siliconchris1973/fairytale/3rd Party Schematics/LED5RG2PIN_Dimension.jpg

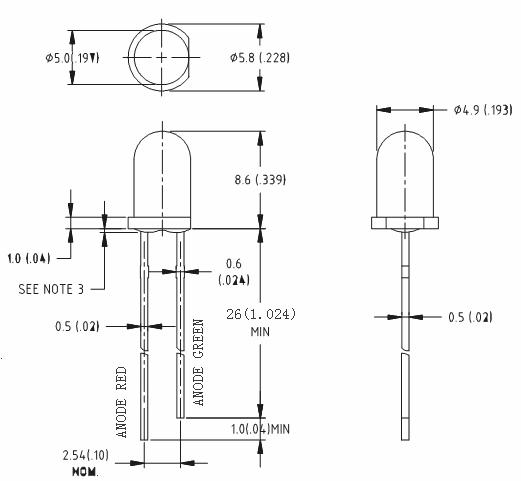
3rd Party Schematics/LED5RG2PIN_Dimension.jpg
