siliconchris1973/fairytale/Pics for V2/NFC-Backside.jpg

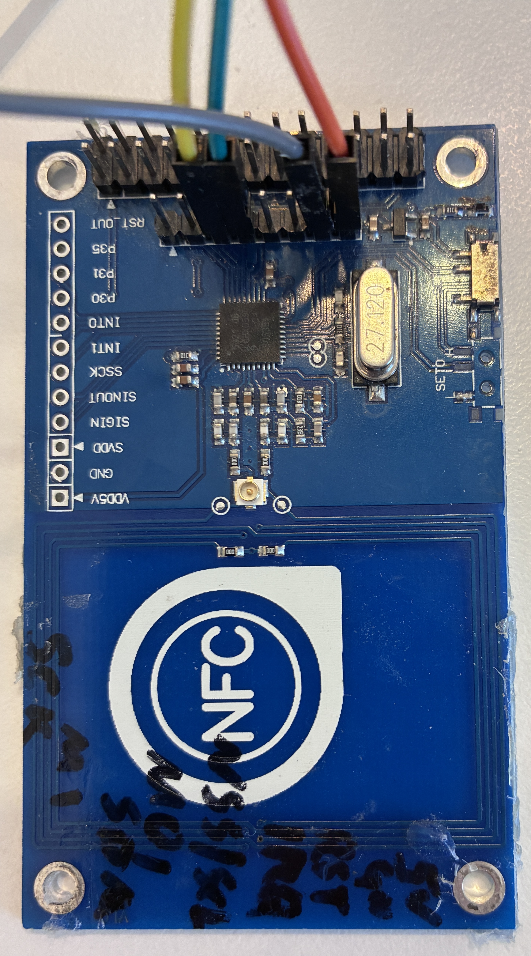
Pics for V2/NFC-Backside.jpg
