siliconchris1973/fairytale/Pics for V2/NFC-V3 hinten.jpg

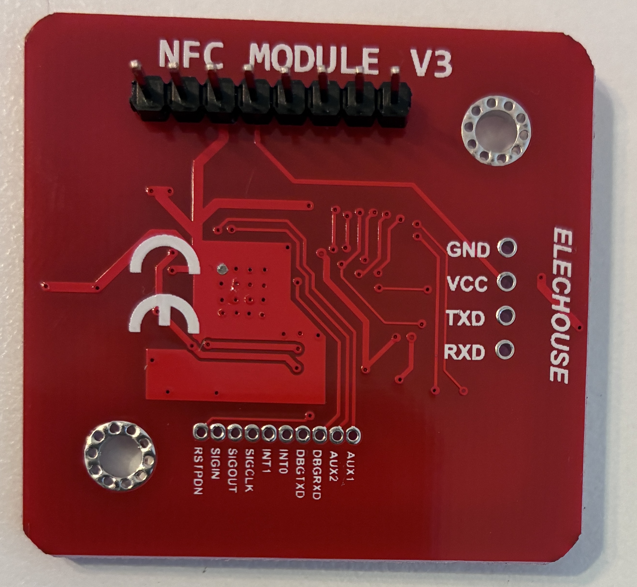
Pics for V2/NFC-V3 hinten.jpg
