siliconchris1973/fairytale/Pics for V2/NFC-V3 vorne.jpg

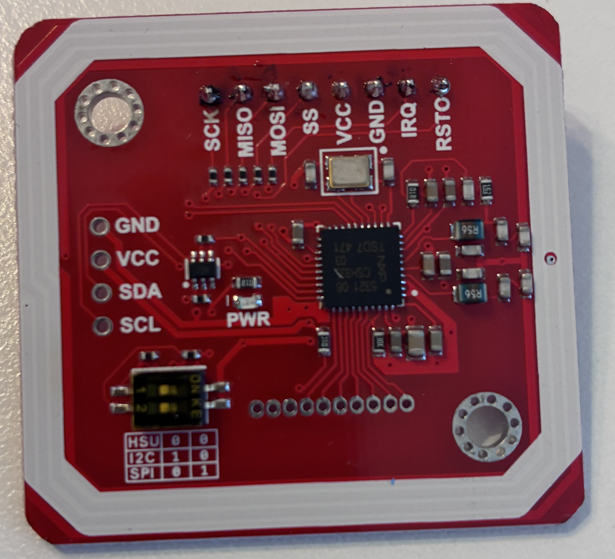
Pics for V2/NFC-V3 vorne.jpg
