siliconchris1973/fairytale/Pics for V2/NFC-Vorderseite.JPG

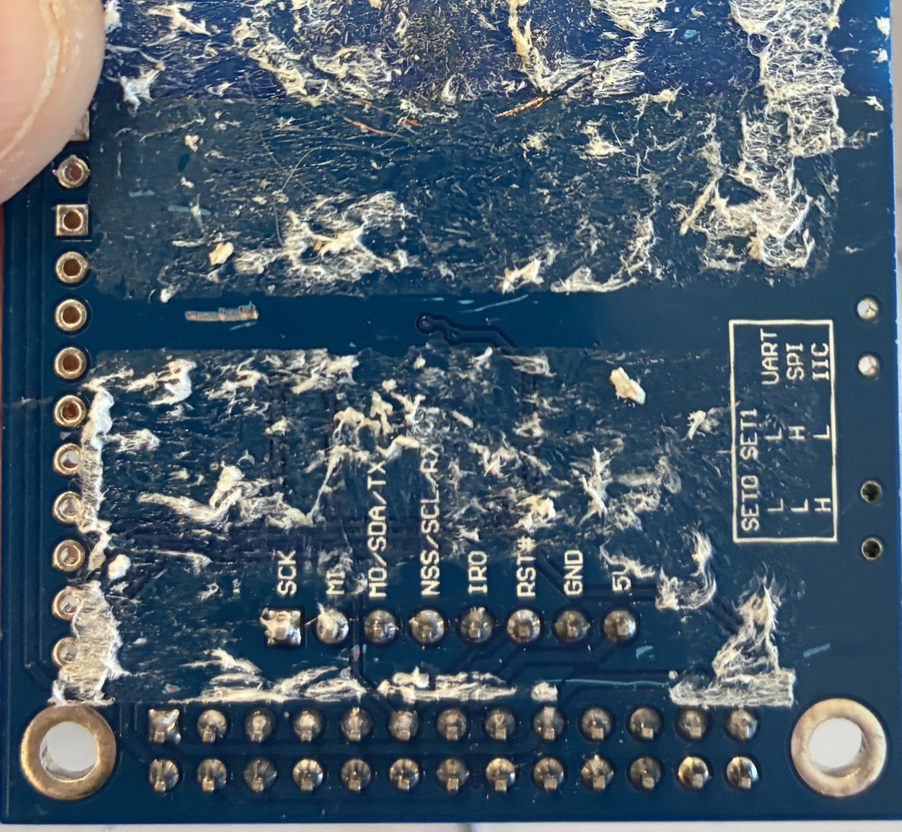
Pics for V2/NFC-Vorderseite.JPG
