siliconchris1973/fairytale/RASPI-stuff/RASPI 3rd Party Tutorials/RDM6300 RFID Reader Schematics.jpg

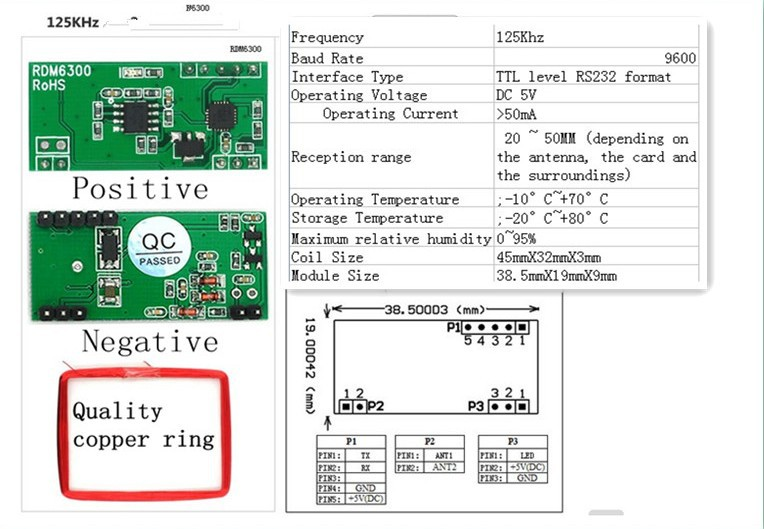
RASPI-stuff/RASPI 3rd Party Tutorials/RDM6300 RFID Reader Schematics.jpg
