siliconchris1973/fairytale/3rd Party Schematics/adafruit music maker pinout.jpg

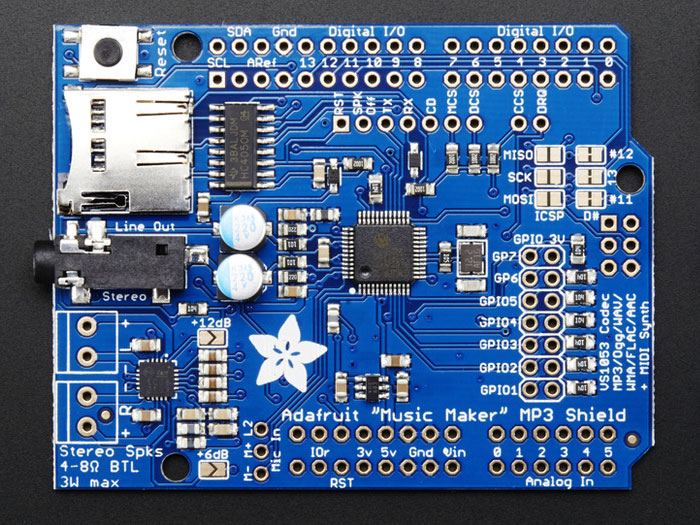
3rd Party Schematics/adafruit music maker pinout.jpg
