siliconchris1973/fairytale/Building Pictures/4 Buttons Wiring.jpg

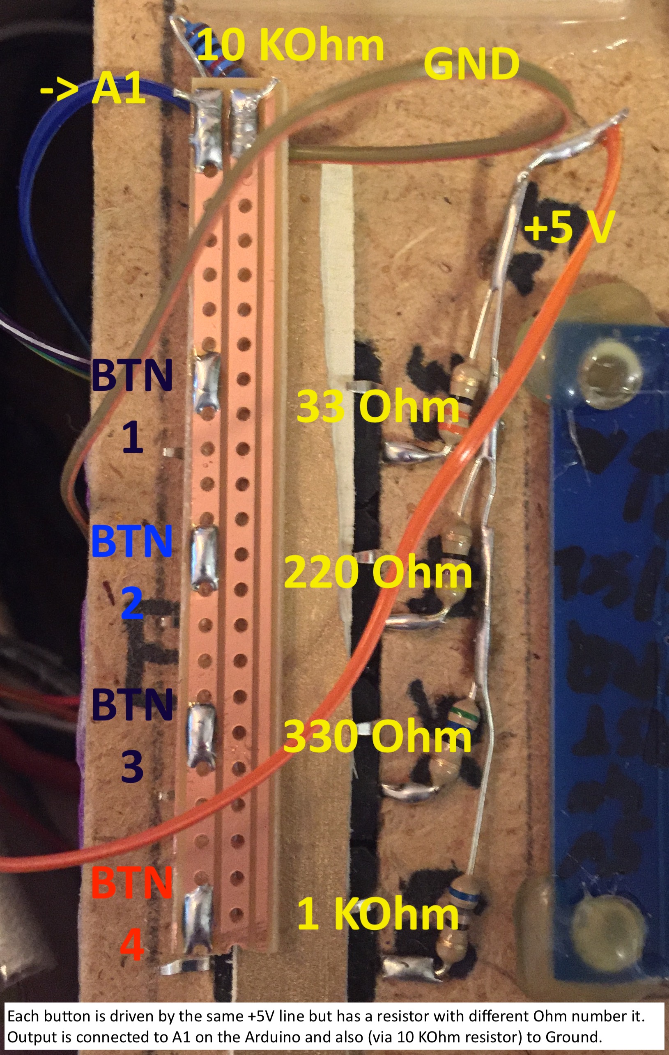
Building Pictures/4 Buttons Wiring.jpg
