siliconchris1973/fairytale/Building Pictures/Back with power outlet and on off switch.jpg

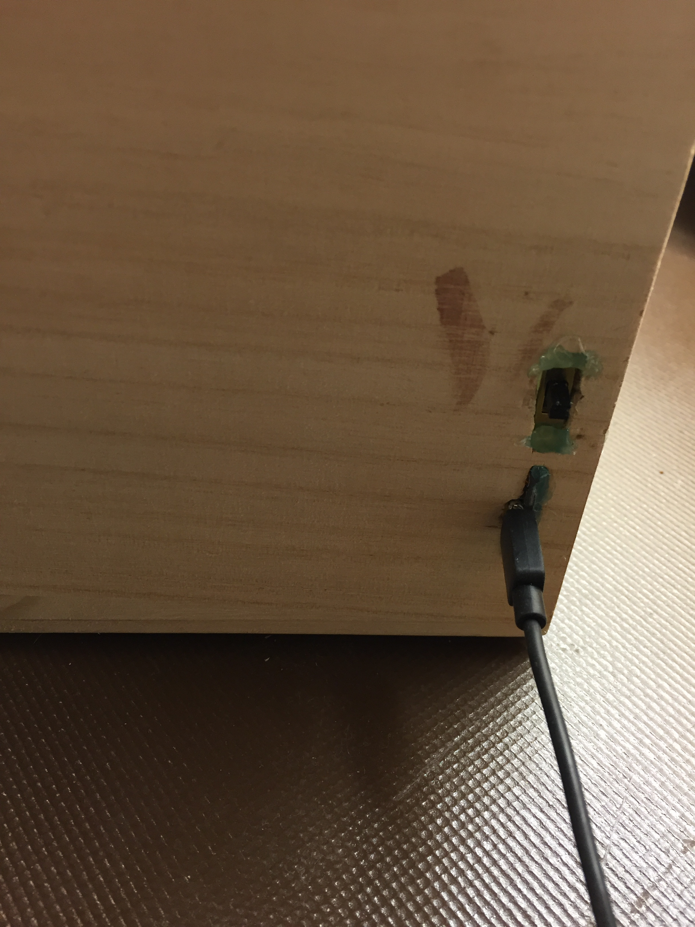
Building Pictures/Back with power outlet and on off switch.jpg
