siliconchris1973/fairytale/Building Pictures/Inner setup with Arduino and power line.jpg

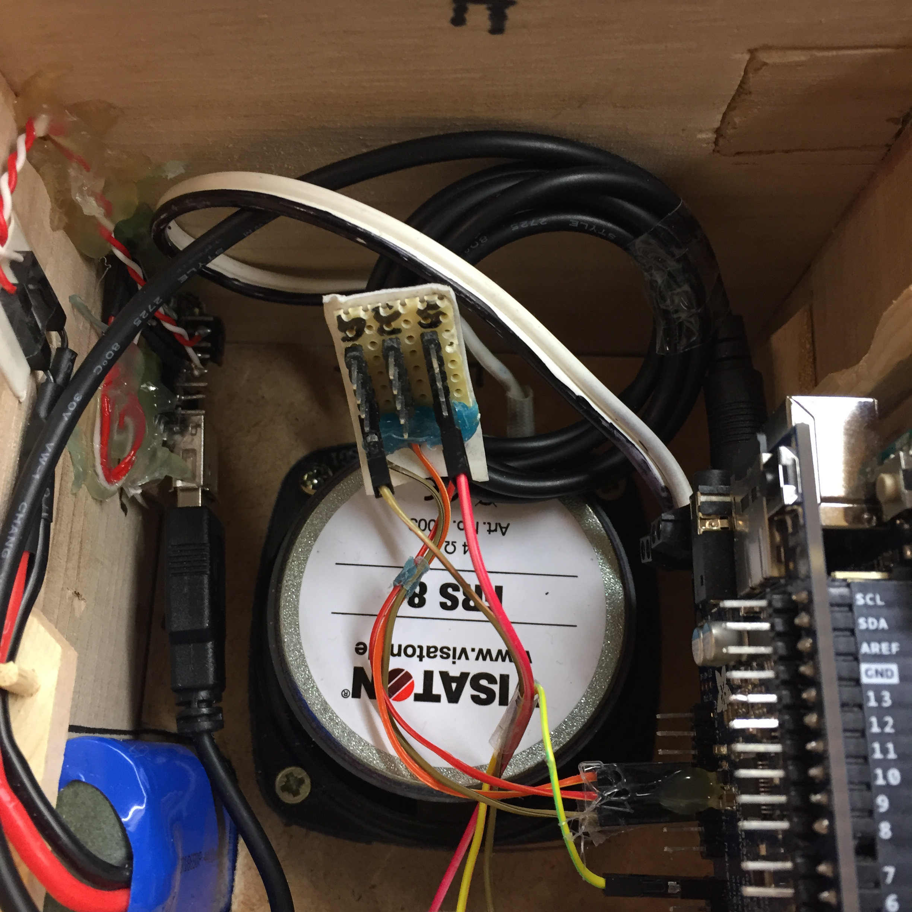
Building Pictures/Inner setup with Arduino and power line.jpg
