siliconchris1973/fairytale/Building Pictures/Inner setup with powerboost BAT Arduino Speaker and Potentiometer.jpg

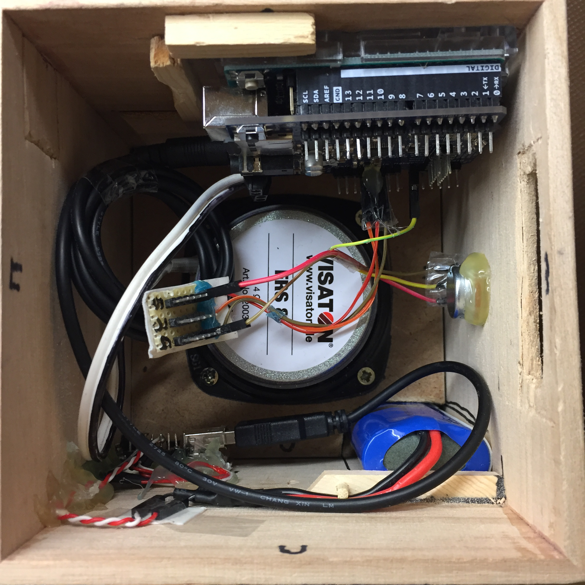
Building Pictures/Inner setup with powerboost BAT Arduino Speaker and Potentiometer.jpg
