siliconchris1973/fairytale/Building Pictures/Inner setup with top plate.jpg

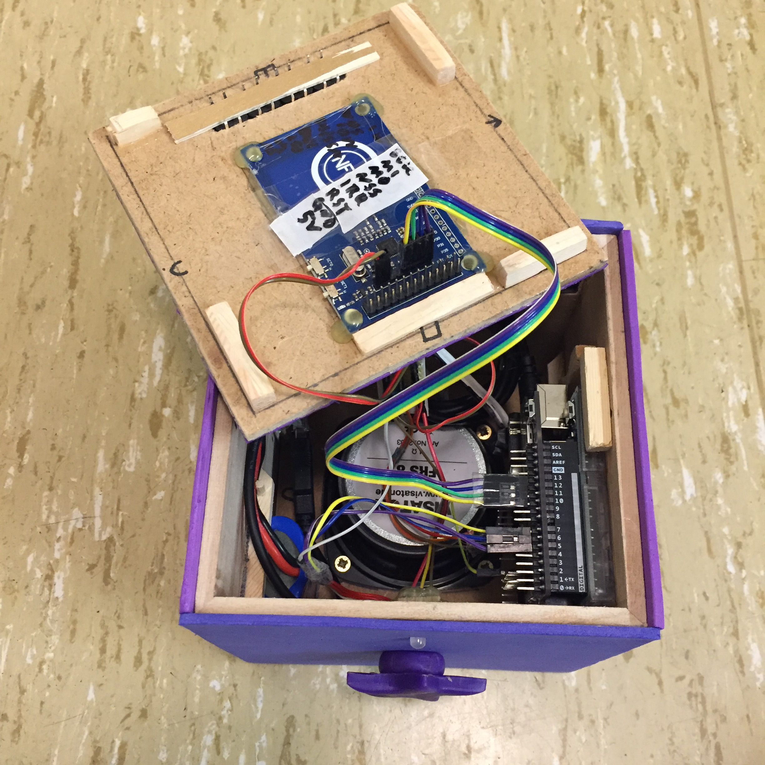
Building Pictures/Inner setup with top plate.jpg
