siliconchris1973/fairytale/Building Pictures/Isometrie back with pwr switch 4 buttons and cutout prog opening.jpg

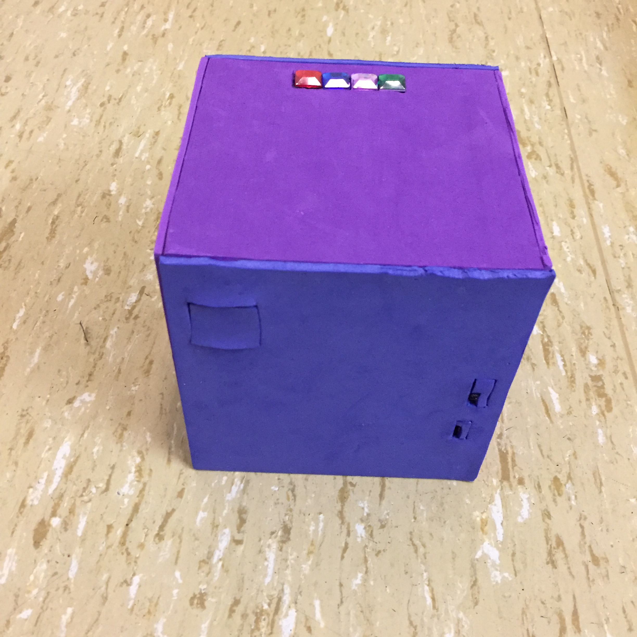
Building Pictures/Isometrie back with pwr switch 4 buttons and cutout prog opening.jpg
