siliconchris1973/fairytale/Building Pictures/PN532 Backside.jpg

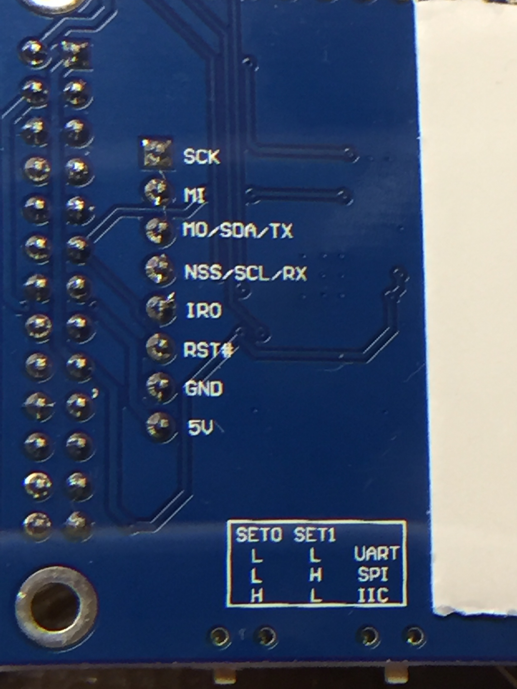
Building Pictures/PN532 Backside.jpg
