siliconchris1973/fairytale/Building Pictures/Potentiometer glued and wired.jpg

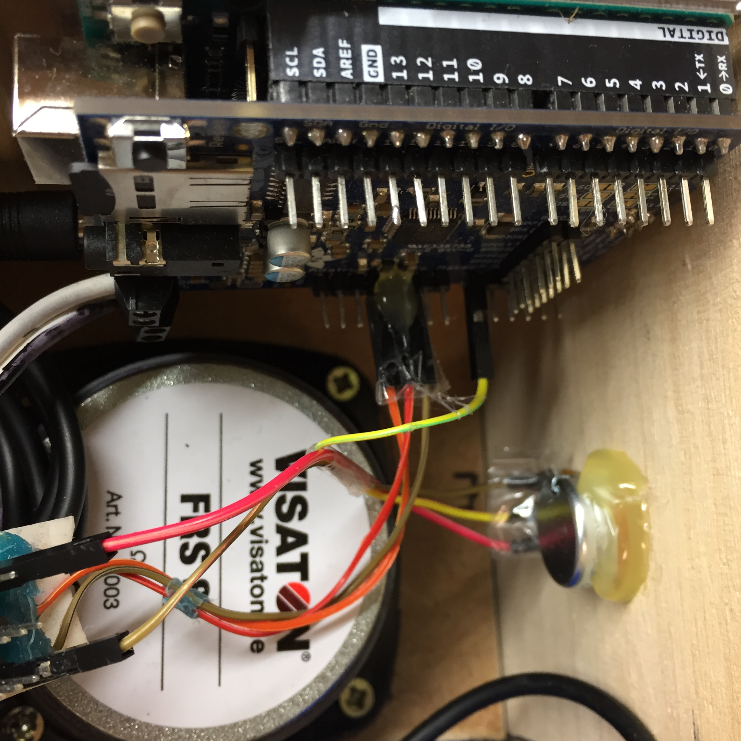
Building Pictures/Potentiometer glued and wired.jpg
