siliconchris1973/fairytale/Building Pictures/Top plate back with PN532 board wired.jpg

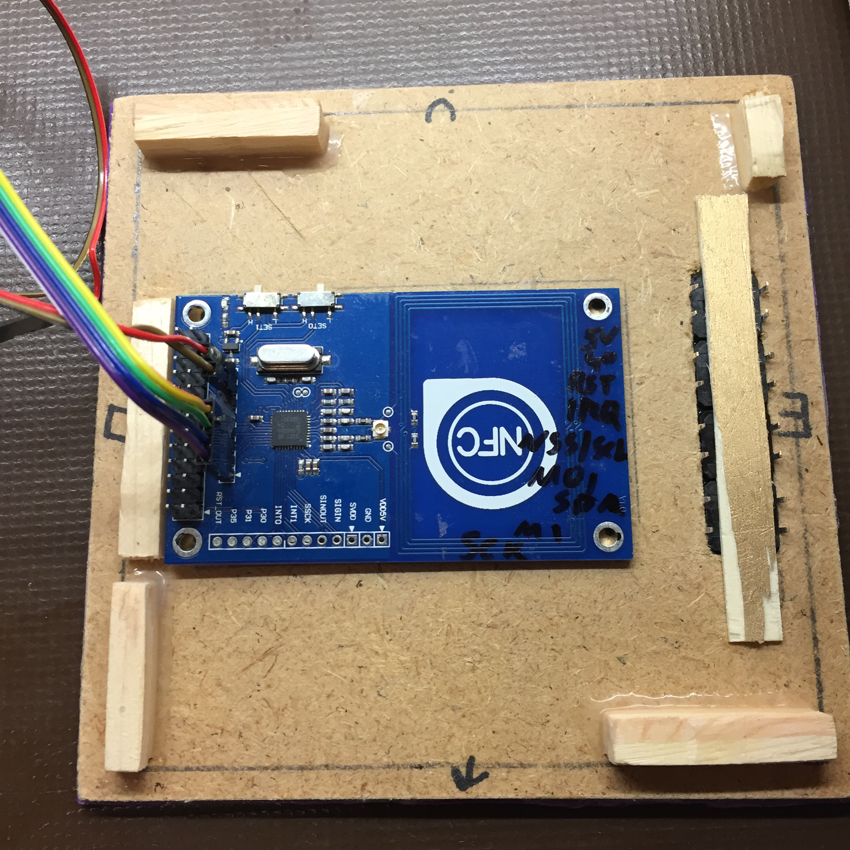
Building Pictures/Top plate back with PN532 board wired.jpg
