siliconchris1973/fairytale/RASPI-stuff/node-codeline/fairytale-app/scripts/startup/image.py

# Copyright (c) 2014 Adafruit Industries
# Author: Tony DiCola
#
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
import time

import Adafruit_Nokia_LCD as LCD
import Adafruit_GPIO.SPI as SPI

from PIL import Image


# Raspberry Pi hardware SPI config:
DC = 23
RST = 24
SPI_PORT = 0
SPI_DEVICE = 0

# Raspberry Pi software SPI config:
# SCLK = 4
# DIN = 17
# DC = 23
# RST = 24
# CS = 8

# Hardware SPI usage:
disp = LCD.PCD8544(DC, RST, spi=SPI.SpiDev(SPI_PORT, SPI_DEVICE, max_speed_hz=4000000))

# Software SPI usage (defaults to bit-bang SPI interface):
#disp = LCD.PCD8544(DC, RST, SCLK, DIN, CS)

# Initialize library.
disp.begin(contrast=60)

# Clear display.
disp.clear()
disp.display()

# Load image and convert to 1 bit color.
image = Image.open('/opt/startup/bootimage.bmp').convert('1')

# Alternatively load a different format image, resize it, and convert to 1 bit color.
#image = Image.open('happycat.png').resize((LCD.LCDWIDTH, LCD.LCDHEIGHT), Image.ANTIALIAS).convert('1')

# Display image.
disp.image(image)
disp.display()

#print('Press Ctrl-C to quit.')
#while True:
#    time.sleep(1.0)
